osolabstech/The20c/Episode2_CLOCK/v03_CLOCK_4Plane/3DModel_CLOCK_BACK.png

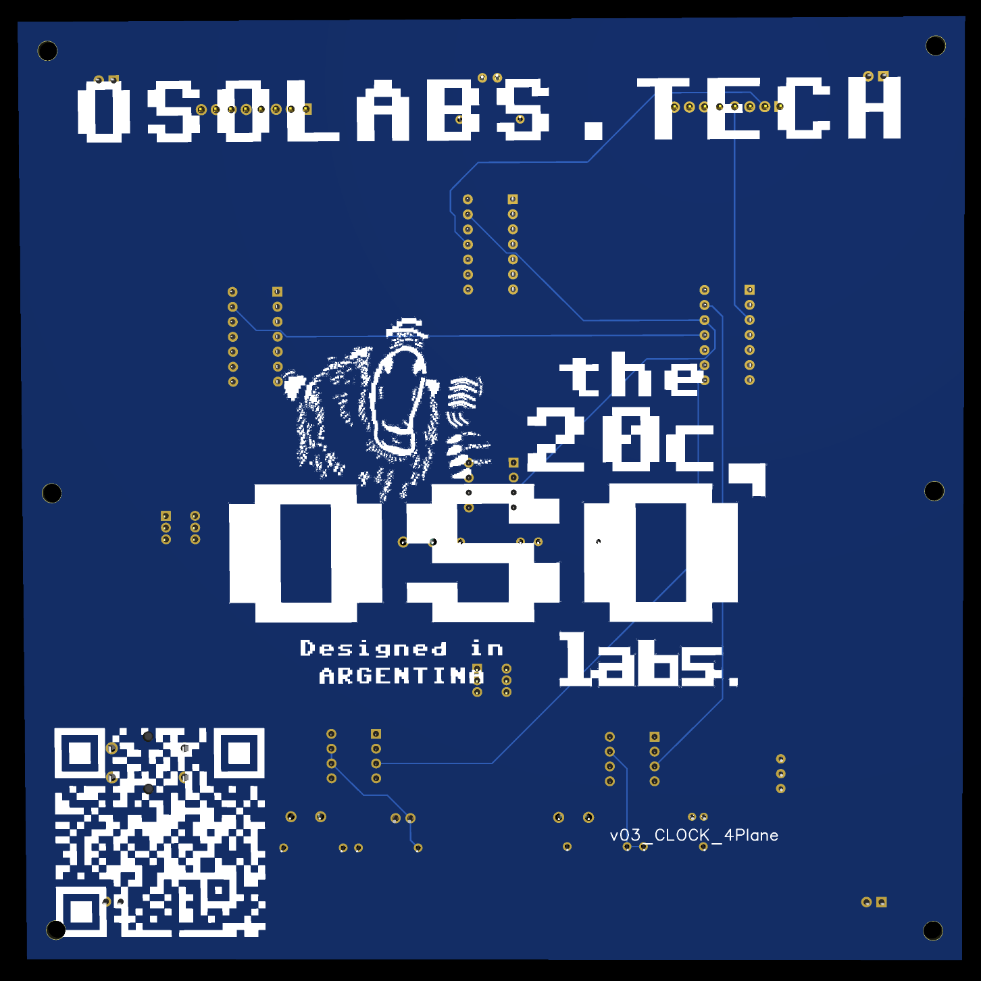
Episode2_CLOCK/v03_CLOCK_4Plane/3DModel_CLOCK_BACK.png
