osolabstech/The20c/Episode3_DUINO_PA/v03_PROTOCOL_ANALYZER_DUINO_4Plane/3DModel_duino_pa_front.png

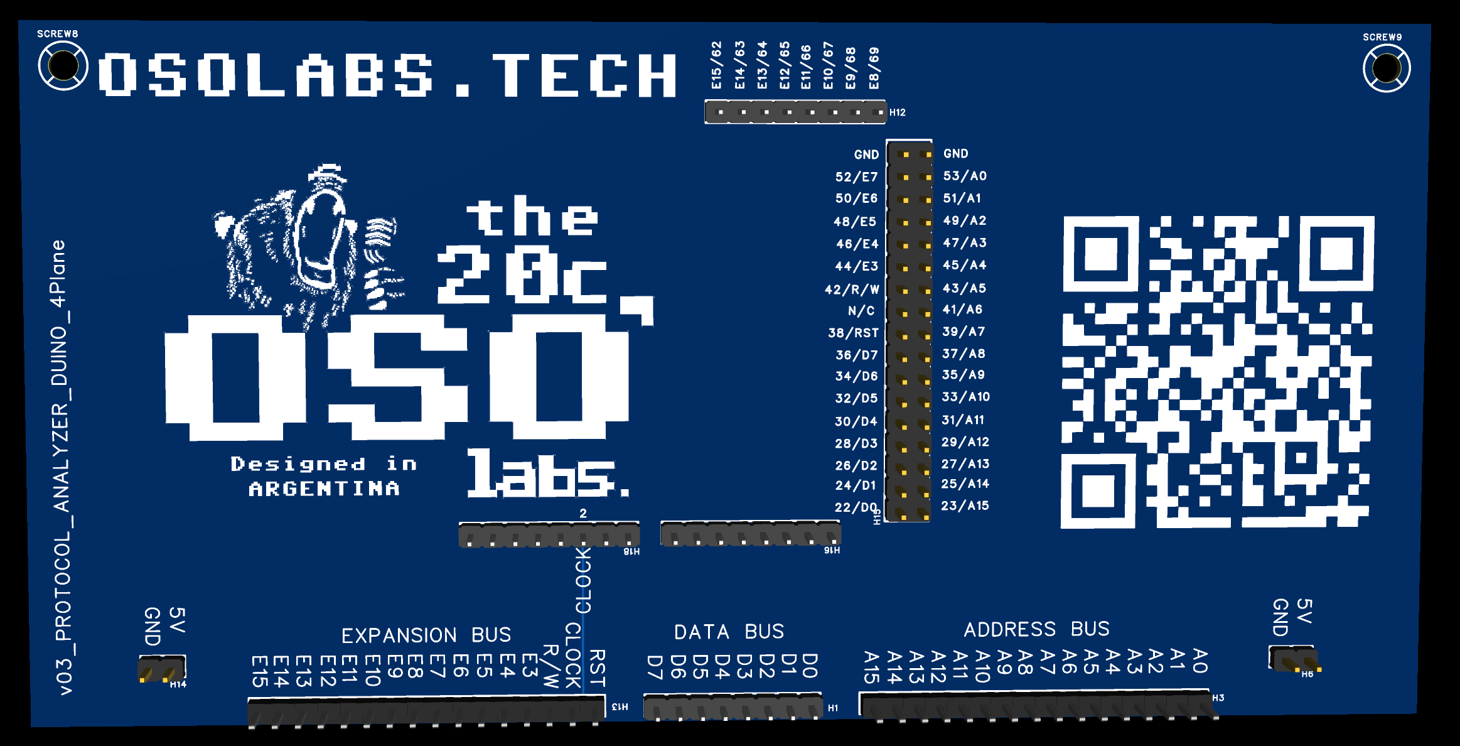
Episode3_DUINO_PA/v03_PROTOCOL_ANALYZER_DUINO_4Plane/3DModel_duino_pa_front.png
