osolabstech/The20c/Episode5_GLUE_LOGIC/pcb/3DModel_GlueLogic_front.png

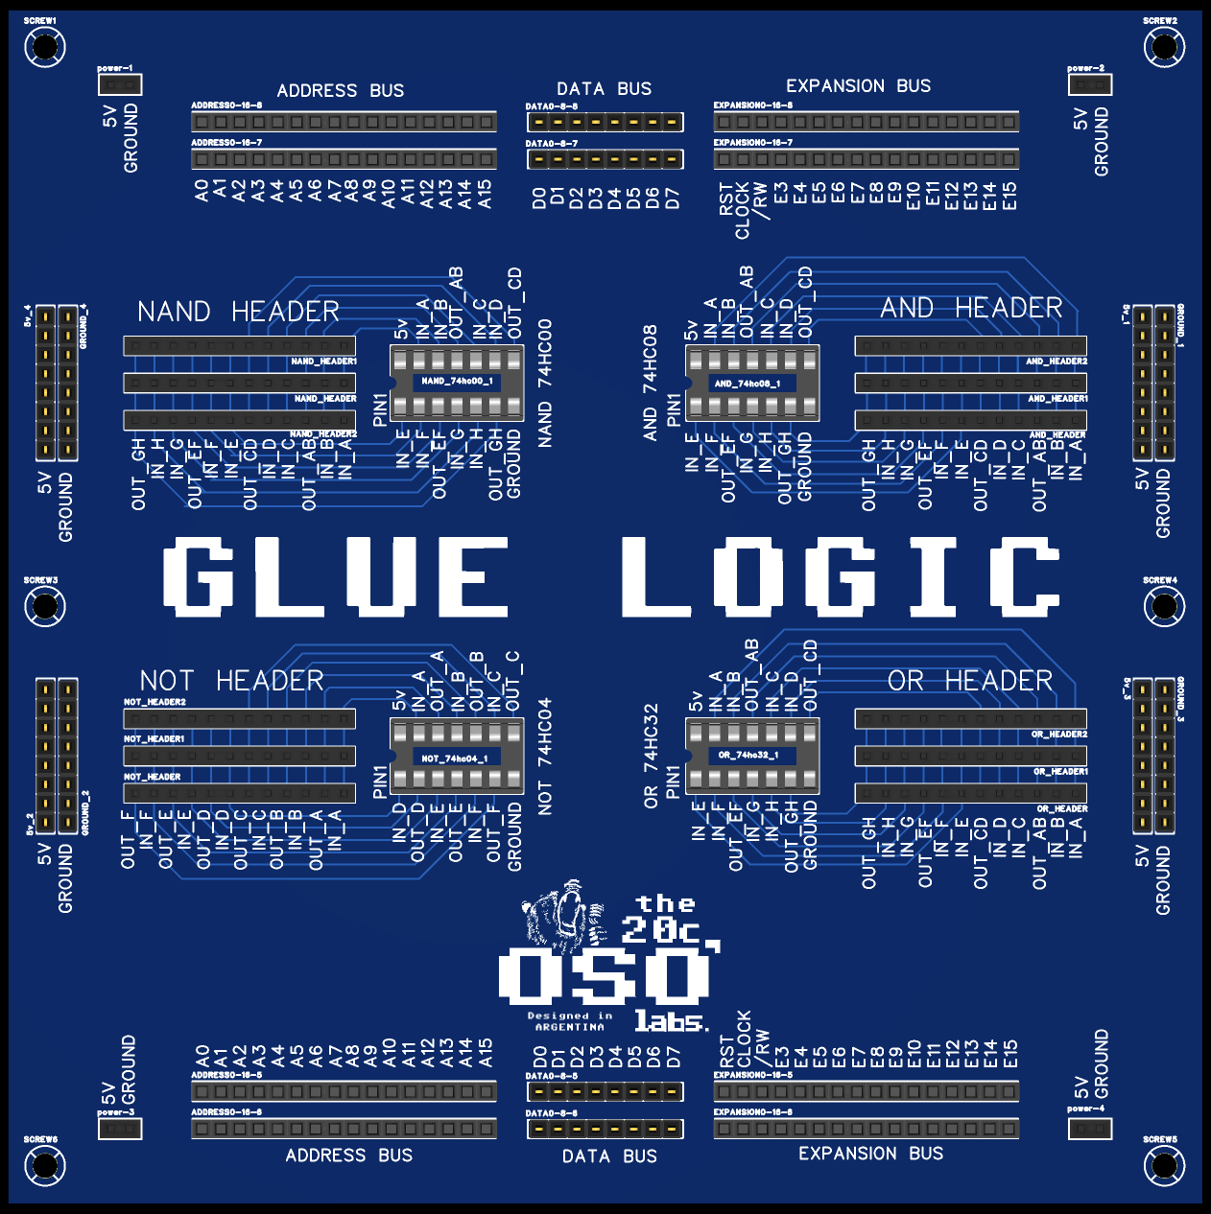
Episode5_GLUE_LOGIC/pcb/3DModel_GlueLogic_front.png
